TurboMarian/BL49/software/BL49/BL49/chip/chip.h

/*
 * chip.h
 *
 * Created: 28.10.2021 15:43:08
 *  Author: Heinrich
 */ 


#ifndef CHIP_H_
#define CHIP_H_

#include "../config.h"
#include "../helpers.h"

void chip_init (void);



#endif /* CHIP_H_ */
