TurboMarian/BL49/software/BL49/BL49/chip/gpio.h

/*
 * gpio.h
 *
 * Created: 28.10.2021 13:42:27
 *  Author: Heinrich
 */ 


#ifndef GPIO_H_
#define GPIO_H_

#include <avr/io.h>
#include <avr/interrupt.h>
#include <stdint.h>
#include <stdbool.h>
#include <string.h>
#include <stdbool.h>
#include "../helpers.h"
#include "../config.h"

typedef struct
{
	uint16_t UA;
	uint16_t UA_calibration;
	uint16_t UR;
	uint16_t UR_calibration;
	uint16_t UBat;
	int16_t URef;
	bool UBat_OK;
	int16_t UOffset;
	int16_t USupply;	
} typeInputs;

extern typeInputs inputs;

void gpio_init (void);
void gpio_read_inputs (typeInputs *inputs);
bool is_ubat_ok (void);
uint16_t calculate_pwm_for_voltage (uint16_t voltage);

#endif /* GPIO_H_ */
